miek770/binary-clock/media/Bottom Layer.png

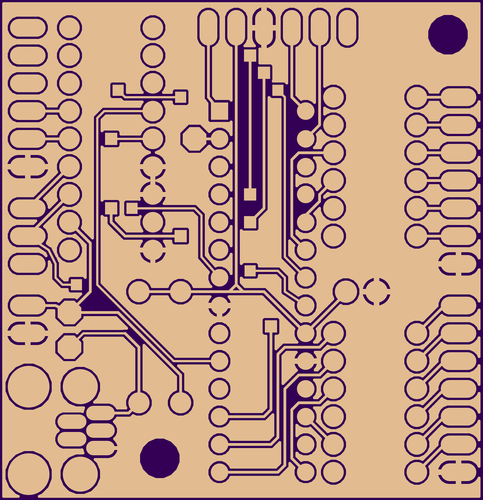
media/Bottom Layer.png
