miek770/binary-clock/media/Drills.png

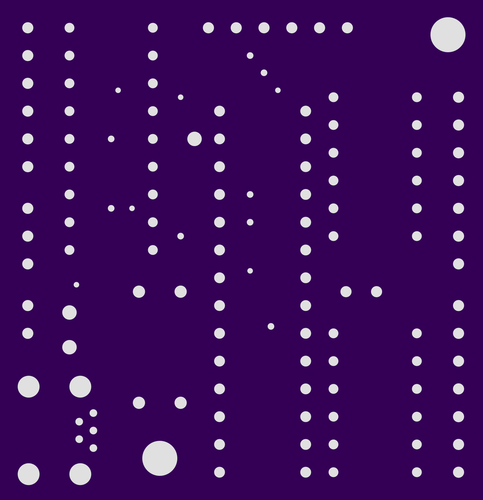
media/Drills.png
