miek770/binary-clock/media/Fichier_002.png

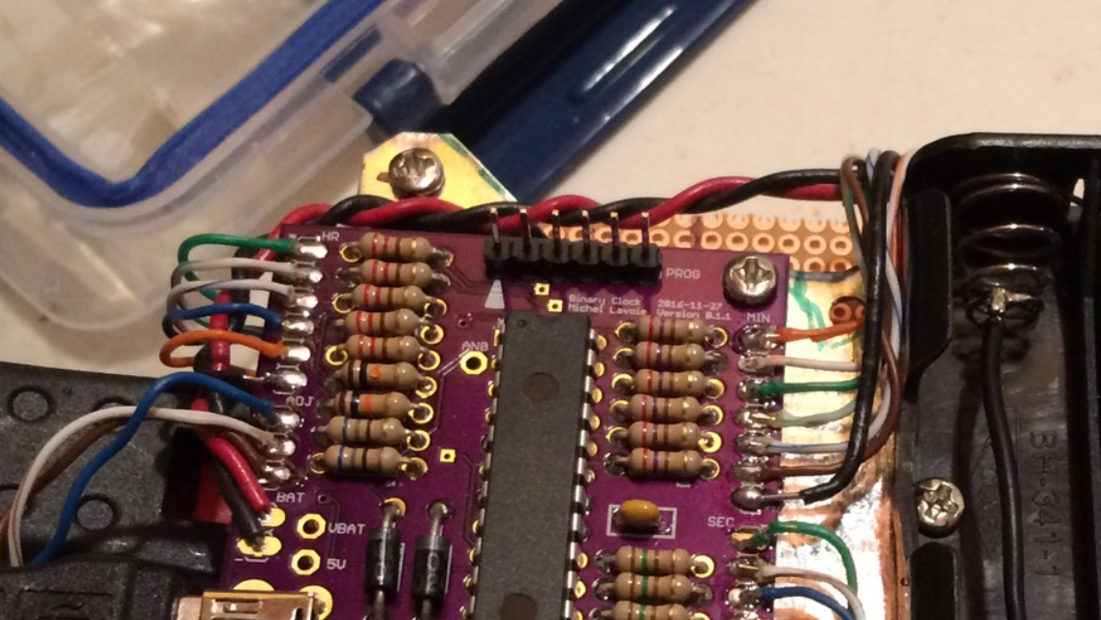
media/Fichier_002.png
