miek770/binary-clock/media/Top Layer.png

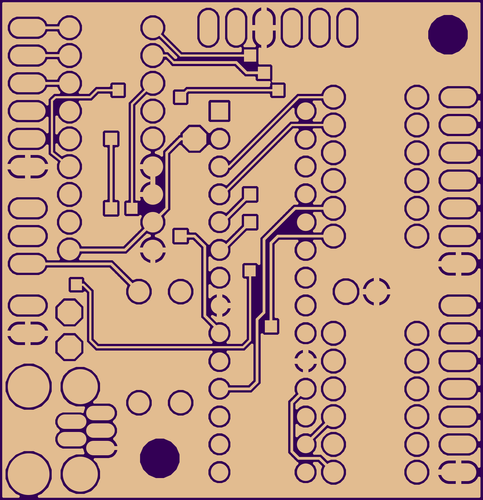
media/Top Layer.png
