miek770/binary-clock/media/Bottom Solder Mask.png

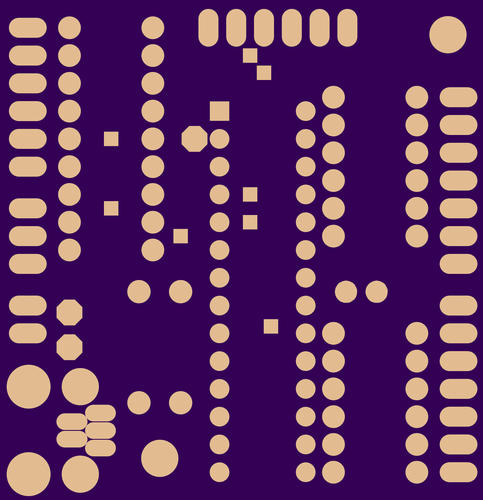
media/Bottom Solder Mask.png
